lbuchman/m1-platform/documentation/Legacy Test Fixture Documentation/Project Notes/Trouble Shooting.docx

# Test Fixture Troubleshooting guide

This document provides information on how to trouble shoot the test fixture.

This document does not provide information on how to troubleshoot or repair M1-3200 boards. For M1-3200 help contact S2 hardware team.

Reference documents:

1. Test board Serial terminal.docx
2. Backend CLI.docx

# Testing the test fixture

The test fixture shall be tested with the know to work “Golden” M1-3200. Please have few Golden boards for the testing.

Run Commission Test from test fixture PC front end GUI application.

If error is reported follow the information below for the troubleshooting guide.

Error which will not produce printed Error labels

1. Hand help scanner issue - check USB cable, replace the scanner
2. Label printer – paper jam, USB cable, power supply, replace the label printer
3. Keyboard or mouse – check the battery, replace
4. Ethernet Error – check cables, check Sam-E, replace SAM-E
5. Test fixture power – check wiring, check power supply, replace power supply
6. USB Hub – verify the Hub is working, check wiring, replace the Hub
7. PC – contact LenelS2
8. PC has incorrect time, or Logs sync issues – check PC internet connection

Printed Error labels

Id | Error Code | Test | Remedy
ICT_EXCEPT | ICT-EXCEPTION | ICT | ICT test unexpected failure. Re-run the test. Contact S2
TP025 | 000000000TP25 | ICT | TP25 voltage is out of tolerance. TP25 voltage is out of tolerance Check wiring, troubleshoot or replace custom test board
TP33 | 000000000TP33 | ICT | TP33 voltage is out of tolerance Check wiring, troubleshoot or replace custom test board
TP35 | 000000000TP35 | ICT | TP35 voltage is out of tolerance Check wiring, troubleshoot or replace custom test board
TP34 | 000000000TP34 | ICT | TP34 voltage is out of tolerance Check wiring, troubleshoot or replace custom test board
TP36 | 000000000TP36 | ICT | TP36 voltage is out of tolerance Check wiring, troubleshoot or replace custom test board
TP31 | 000000000TP31 | ICT | TP31 voltage is out of tolerance Check wiring, troubleshoot or replace custom test board
J5.13 | 000000TPJ5.13 | ICT | Ribbon Cable J5.13 voltage is out of tolerance Check wiring, troubleshoot or replace custom test board
J5.8 | 0000000TPJ5.8 | ICT | Ribbon Cable J5.8 voltage is out of tolerance Check wiring, troubleshoot or replace custom test board
BatCellBat | 000000CoinBat | ICT | Coin Cell backup battery voltage is out of tolerance Check wiring, troubleshoot or replace custom test board
J5.18 | 000000TPJ5.18 | ICT | Ribbon Cable continuity failed Check wiring, troubleshoot or replace custom test board
J5.15 | 000000TPJ5.15 | ICT | Ribbon Cable continuity failed Check wiring, troubleshoot or replace custom test board
J5.17 | 000000TPJ5.17 | ICT | Ribbon Cable continuity failed Check wiring, troubleshoot or replace custom test board
J5.19 | 000000TPJ5.19 | ICT | Ribbon Cable continuity failed Check wiring, troubleshoot or replace custom test board
J5.16 | 000000TPJ5.16 | ICT | Ribbon Cable continuity failed Check wiring, troubleshoot or replace custom test board
J5.5 | 0000000TPJ5.5 | ICT | Ribbon Cable voltage is out of tolerance Check wiring, troubleshoot or replace custom test board
J5.6 | 0000000TPJ5.6 | ICT | Ribbon Cable voltage is out of tolerance Check wiring, troubleshoot or replace custom test board
J5.7 | 0000000TPJ5.7 | ICT | Ribbon Cable voltage is out of tolerance Check wiring, troubleshoot or replace custom test board
J5.14 | 000000TPJ5.14 | ICT | Ribbon Cable voltage is out of tolerance Check wiring, troubleshoot or replace custom test board
J5.23 | 000000TPJ5.23 | ICT | Ribbon Cable voltage is out of tolerance Check wiring, troubleshoot or replace custom test board
J5.25 | 000000TPJ5.25 | ICT | Ribbon Cable voltage is out of tolerance Check wiring, troubleshoot or replace custom test board
J5.20 | 000000TPJ5.20 | ICT | Ribbon Cable voltage is out of tolerance Check wiring, troubleshoot or replace custom test board
J5.22 | 000000TPJ5.22 | ICT | Ribbon Cable voltage is out of tolerance Check wiring, troubleshoot or replace custom test board
J5.24 | 000000TPJ5.24 | ICT | Ribbon Cable voltage is out of tolerance Check wiring, troubleshoot or replace custom test board
J5.26 | 000000TPJ5.26 | ICT | Ribbon Cable voltage is out of tolerance Check wiring, troubleshoot or replace custom test board
J8.2 | 0000000RedLed | ICT | J8.2 Red Led voltage drop is out of tolerance Check wiring, troubleshoot or replace custom test board
J8.1 | 0000000BlueLed | ICT | J8.1 Blue Led voltage drop is out of tolerance Check wiring, troubleshoot or replace custom test board
RS422 | 00000000RS422 | ICT | Ribbon Cable RS-422 echo test failed Check wiring, troubleshoot or replace custom test board
RS485 | 00000000RS485 | ICT | RS-485 echo test failed Check wiring, troubleshoot or replace custom test board
Tamper Pin | 0000000Tamper | ICT | Tamper pin test failed Check wiring, troubleshoot or replace custom test board
DDR3Bus | 0000DDR3-DBus | ICT | DDR3 data bus test failed Check wiring, troubleshoot or replace custom test board
DDR3ABus | 0000DDR3-ABus | ICT | DDR3 address bus test failed. This is not test fixture related error
DDR3 | 000000000DDR3 | ICT | DDR3 read/write verify test failed. This is not test fixture related error
EEPROM | 0000000EEPROM | ICT | EEPROM test failed
EEPROMUPDATE | 00UPD-0EEPROM | ICT | Update EEPROM with new data command failed. This is not test fixture related error
ATOP | 00BATT-SWITCH | ICT | Test Main power to battery power switching failed. Check wiring, troubleshoot or replace custom test board
BACH | 000BATT-CHARG | ICT | The Battery module charging voltage is out of tolerance. Check wiring, troubleshoot or replace custom test board
STM | 000000USB-DFU | ICT | Failed to program M1 bootstrap STM, RFU issue or BUT is down
APP80 | 00000APP-PING | APP | BUT Web server is down, possible APP is not running. This is not test fixture related error
FLASH | 0000000000FLASH | FLASH | Program FLASH failed. Check M1-3200 USB cable
MAC | 000000PROG-AMC | MAC | Program MAC failed. Check M1-3200 USB cable
MAC_CMP_ERR | 000MAC_CMP_ERR | FUN | If config reported MAC does not match OTP MAC This is not test fixture related error
PEN_DRIVE | 00000PEN_DRIVE | FUN | Pen drive failed. BUT USB Host port issue. Check USB cable. Replace Pen drive
RTC | 00000000000RTC | FUN | RTC test failed. This is not test fixture related error
SPI_RAM | 0000000SPI_RAM | FUN | SPI RAM test failed. This is not test fixture related error
FUN_EXCEPT | FUN-EXCEPTION | FUN | Functional test general failure. Contact LenelS2
WDT | 0000000000WDT | FUN | Watchdog test failed. This is not test fixture related error
BUT_ETHER | 0000UUT_ETHER | FUN | BUT not pingable, possibly Ethernet controller or cabling issue
BUT_TERM | 00000UUT_TERM | FUN | BUT terminal login error, check serial link, check FW/SW revisions. Replace USB cable, Replace RS232 to USB cable
SSH_BRECON | 0000SSH_BRECON | FUN | Ssh connection to BUT error, check wiring or cabling issue.
RFU_STM | 000000DFU_STM | FUN | Program bootstrap STM file to BUT over RFU error. Check wiring, replace M1-3200 USB cable
I2CBus1 | 00000I2C_BUS1 | FUN | I2C Bus 1 test failed. This is not test fixture related error
I2CBus02 | 0000I2C_BUS02 | FUN | I2C Bus 0,2 test failed. This is not test fixture related error
NO_OTP_MAC | 000NO_OTP_MAC | FUN | MAC Address is not programmed in OTP. This is not test fixture HW related error
SERIAL_MISMATCH | SER_MISS_MATCH | LABEL | Serial number provided does not match EEPROM value. Invalid serial number scanned in
FW_MISMATCH | FW_MISS_MATCH | LABEL | The BUT programmed FW Rev does not match FW File. Re-Commission the M1-3200
Lever Sensor | #NAME? | ICT | The Lock Lever is not locked
ERR_UNDER | 0000ERR_UNDER | Label | Undefined error, i.e. no error code available in the DB for this failure. Contact LenelS2
