lbuchman/m1-platform/documentation/Legacy Test Fixture Documentation/Project Notes/Testing Procedure.docx

Testing Procedure

1. Start the test fixture software

Double click M1-3200 launcher icon on the left side of the Desktop screen

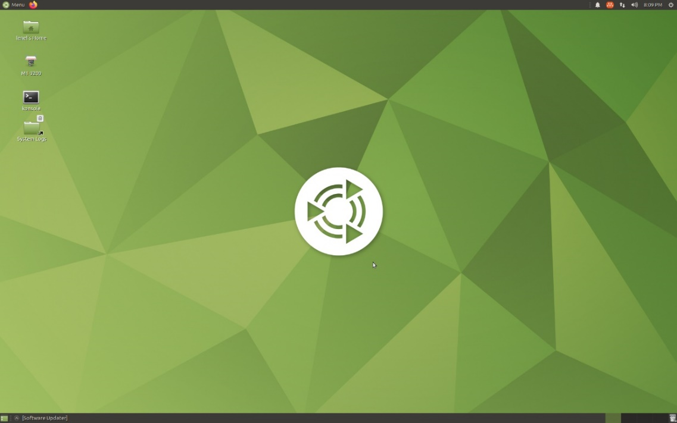
[picture p12: figure]
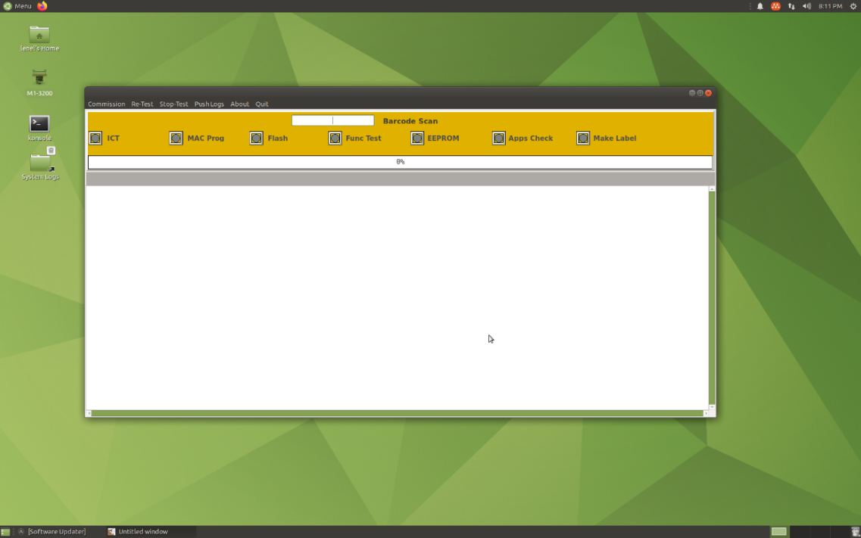
[picture p13: figure]

2. Open the test fixture cover.

Move the cover lever on the right site to the vertical position.

Using the cover handle on the front side of the fixture open the top cover

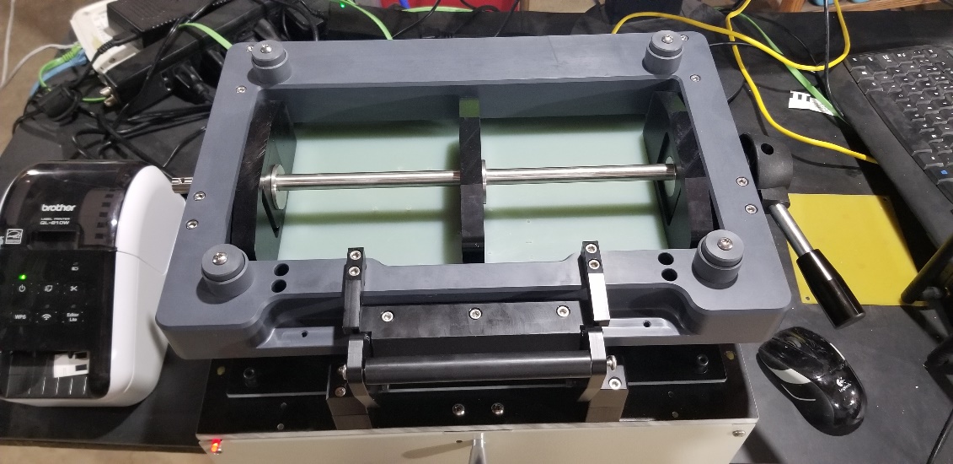
[picture p14: figure]
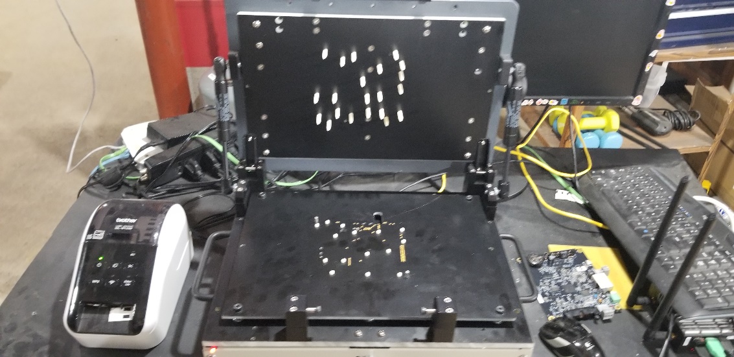
[picture p15: figure]

3. Place the M1-3200 board into the test fixture

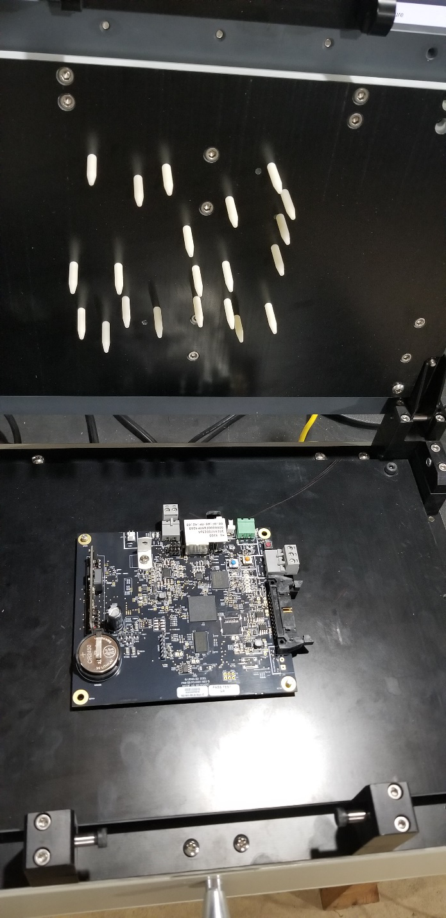
[picture p16: figure]

4. Scan the Serial Number barcode (the board front edge as shown above)

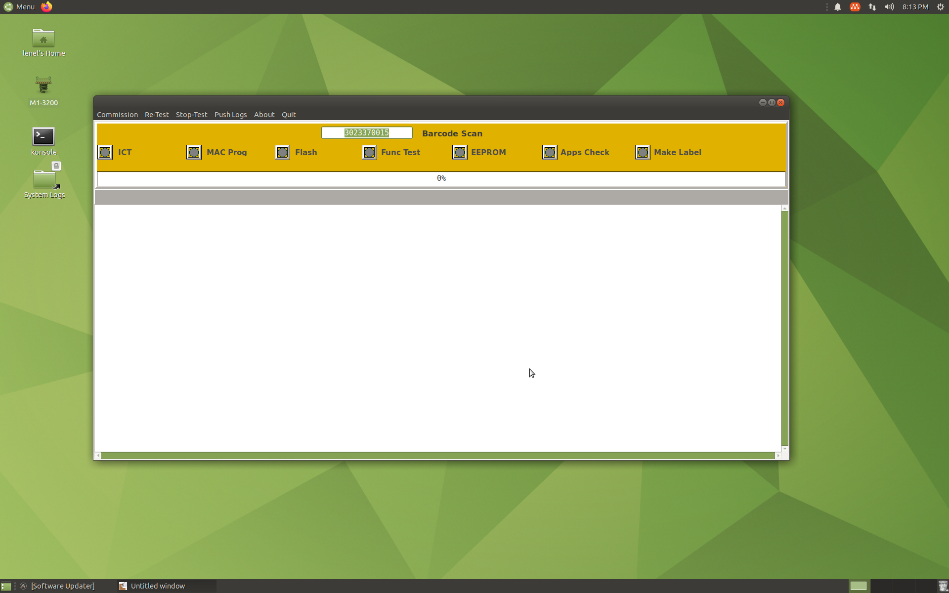
[picture p17: figure]

5. Close the test fixture cover.

Make sure to latch the lever handle on the side of the test fixture to the horizontal position.

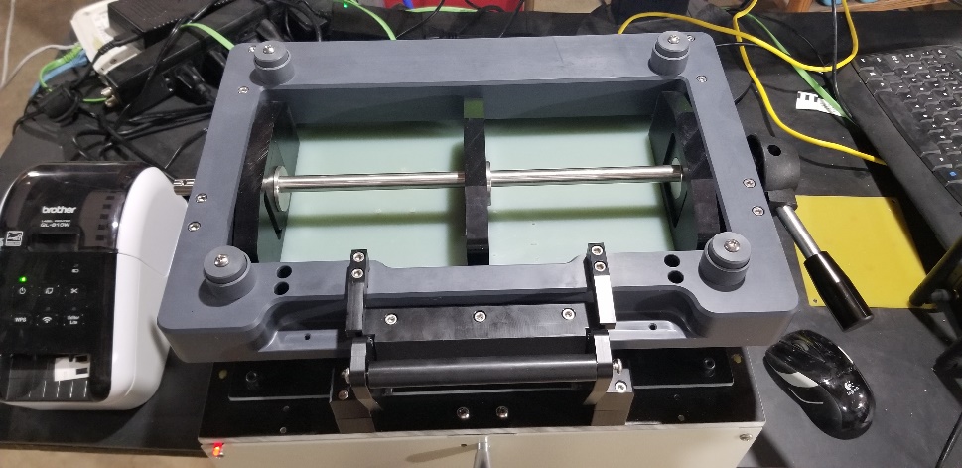
[picture p18: figure]

The Red LED shall be on when the latch lever is locked.

6. Press the desired action, Commission or Re-Test

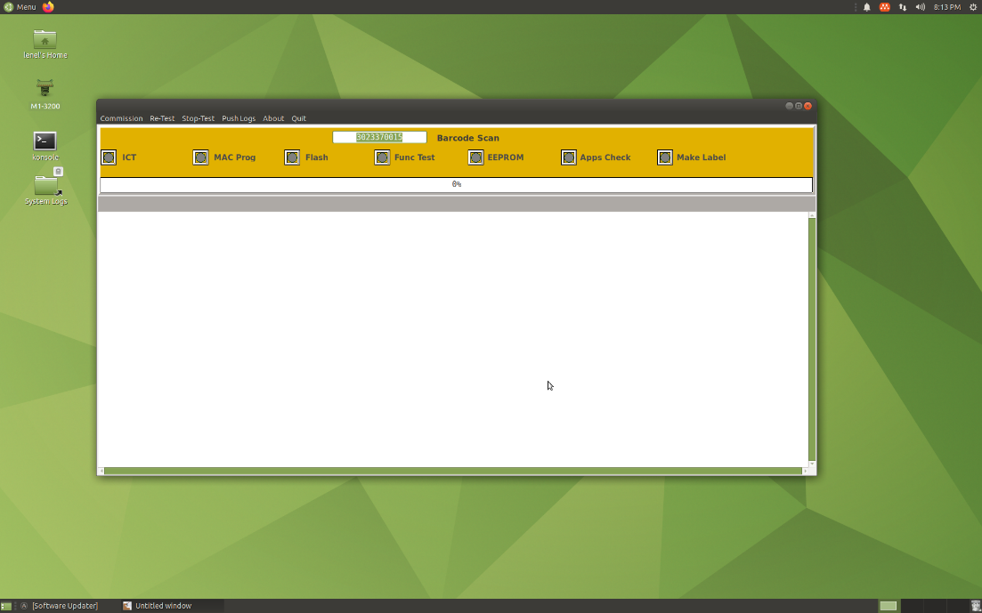
[picture p19: figure]

7. Wait until test is complete

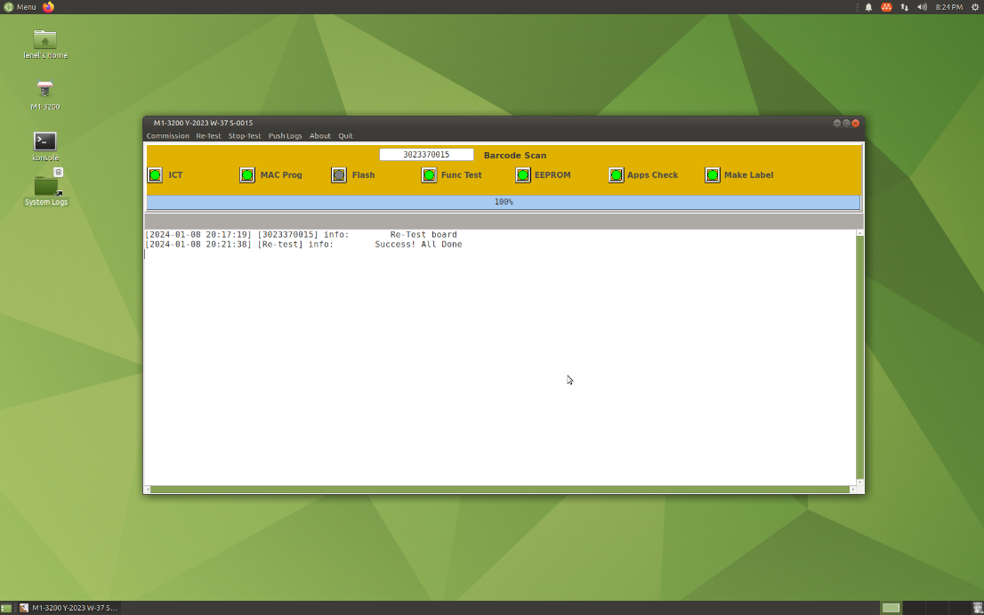
[picture p20: figure]

When complete the label is printed
