lbuchman/m1-platform/documentation/Legacy Test Fixture Documentation/Project Notes/TestPlan.xlsx

Sheet: Test Vectors
Notes | Test Vector # | Description | Purpose | UUT | Test Steps | Expected Result | Test Status
 | 1 | Pogo Pins Inspection | Visual Inspection |  | Open test fixture cover | There are no shorts between pogopins, wiring connections to pogo pins are secured. Wiring to test board terminals are robust. Wiring is well organized to harnesses. Use test fixture 1 pictures as a reference.
 | 2 | TF Wiring inspection | Visual Inspection |  | Open test fixture cover | The power supply wiring are secured and robust. No floating cables, ar connections are robust
Aggregated 42 test cases | 3 | Assembly integrity | Validate the pogo pins are connected to the proper I/O on the test board i.e. verifying the integrity of the electrical connections. There are 5 dozen of connections to check. This is time consuming operation. |  | Use multimeter and set it to the continuity function | Use Wiring map Tab and make sure all connection are correctly made.
 | 45 | Lever Switch test | Lever and Green Led test | Golden Board | 1. Lock the test fixture cover with the Lever handle 3. Execute Re-Test | The Green Led on the front panel of the test fixture shall be on. There shall be no error when test starts that Lever shall be locked before the test
 | 46 | Lever Switch test | Lever and Green Led test | Golden Board | 1. Do not Lock the test fixture cover with the Lever handle 3. Execute Re-Test | The error shall be reported that Lever is not locked
 | 47 | Power supply check | Correct power supply output |  | Use meter and measure power supply 12V and 5V output | The 12V output shall be at least 12.4V, 5V output shell be 5% accurate
 | 48 | Ethernet Internet Connection | Validate the cable is plugged from the PC to the TF | Golden Board | 1. Place the golden board into the fixture. 2. Disconnect ISP Ethernet cable from the PC 3. Execute Re-Test 4. When ICT Test Complete click Stop-Test | [2024-03-01 00:18:44] [3023200040, ict] error: Ethernet Internet jack is not plugged. Check connection and retry the test.
 | 49 | Ethernet Internet Connection | Validate the cable is plugged from the PC to the TF | Golden Board | 1. Place the golden board into the fixture. 2. Connect ISP Ethernet cable from the PC 3. Execute Re-Test 4. When ICT Test Complete click Stop-Test | No Error shall be reported
 | 50 | Ethernet PC/TF Connection | Validate the cable is plugged | Golden Board | 1. Place the golden board into the fixture. 2. Disconnect Ethernet cable from the TF 3. Execute Re-Test 4. When ICT Test Complete click Stop-Test | [2024-03-01 00:18:44] [3023200040, ict] error: M1-3200 Ethernet jack is not plugged. Check connection and retry the test.
 | 51 | Ethernet PC/TF Connection | Validate the cable is plugged | Golden Board | 1. Place the golden board into the fixture. 2. Connect Ethernet cable from the TF 3. Execute Re-Test 4. When ICT Test Complete click Stop-Test | No Error shall be reported
 | 52 | Label Printer Connection | Validate the cable is plugged | Golden Board | 1. Place the golden board into the fixture. 2. Disconnect label printer cable from the PC 3. Execute Re-Test 4. When ICT Test Complete click Stop-Test | [2024-03-01 01:07:24] [3023200040, ict] error: Label Printer is not detected. Check connections and power and retry the test.
 | 53 | Label Printer Connection | Validate the cable is plugged | Golden Board | 1. Place the golden board into the fixture. 2. Connect label printer cable from the 3. Execute Re-Test 4. When ICT Test Complete click Stop-Test | No Error shall be reported
 | 54 | Test Board Usb Link (Teensy connection) | Validate test board (Teensy board) is connected to the PC | Golden Board | 1. Place the golden board into the fixture. 2. Disconnect Teensy USB cable from the PC 3. Execute Re-Test 4. When ICT Test Complete click Stop-Test | [2024-03-01 23:24:06] [3023200040, ict] error: Test board Teensy is not found. Check connections and retry the test.
 | 55 | Test Board Usb Link (Teensy connection) | Validate test board (Teensy board) is connected to the PC | Golden Board | 1. Place the golden board into the fixture. 2. Connect Teensy USB cable to the PC 3. Execute Re-Test 4. When ICT Test Complete click Stop-Test | No Error shall be reported
Only USB to RS232 cable is tested by this test. | 56 | Test M1-3200 terminal serial link | Validate that USB to RS232 converter for M1-3200 terminal | Golden Board | 1. Place the golden board into the fixture. 2. Disconnect USB to RS232 cable from the PC 3. Execute Re-Test 4. When ICT Test Complete click Stop-Test | [2024-03-01 23:24:06] [3023200040, ict] error: M1-3200 Terminal Serial Converter is not found. Check connections and retry the test.
Only USB to RS232 cable is tested by this test. | 57 | Test M1-3200 terminal serial link | Validate that USB to RS232 converter for M1-3200 terminal | Golden Board | 1. Place the golden board into the fixture. 2. Connect USB to RS232 cable to the PC 3. Execute Re-Test 4. When ICT Test Complete click Stop-Test | No Error shall be reported
 | 58 | Cloud synch alert | Validate the GUI frontend displays alert is activated if logfiles are not synced to the Cloud | Golden Board | 1. Remote flagging file with the command: #sudo rm -f /home/lenel/m1mtf/*.txt. 2. Wait up to 1 min | The GUI shall display the blinking alert in Red in the upper left cornet. The warning shall read "Cloud Sync Failed for 7 days, contact LenelS2
 | 59 | Manual Cloud synch | Validate the GUI frontend displays alert is deactivated if logfiles are synced to the Cloud | Golden Board | 1. Execute test vector 11 2. Click main menu->Cloud->Push Logs 3. Click main menu->Cloud->Push Secrets | Wait up to 1 min, the blinking Red alert shall not be disabled
 | 60 | Automatic Cloud sync | Validate that logfiles and secrets are automatically updated qat night. | Golden Board | Execute test vector 11 | Wait overnight. Next day the blinking Red alert shall not be disabled
 | 61 | Serial Number validation | Validate the serial number entered is properly formatted | Golden Board | 1. Scan the serial number from M1-3200 2. Execute Re-Test | No Error shall be reported
 | 62 | Serial Number validation | Validate the serial number entered is properly formatted | Golden Board | 1. Enter 10 digits for the serial number, make sure the first two are not 30 2. Execute Re-Test | The Error pop-up with the message :Invalid Barcode" shall be displayed.
 | 63 | Duplicate serial number | Validate that serial number is unique | Golden Board | 1. Scan the serial number from M1-3200 2. Execute Re-Test 3. When ICT Test Complete click Stop-Test 4. Replace the Golden Board with another Golden board 5. Do not change the serial number 6. Execute Re-Test | The command shall failed with the message below. Executing program MAC command ... [2024-03-02 02:11:06] [3023200040, progmac] error: UNIQUE constraint failed: records.cpuSerial
 | 64 | PC SW update | Validate the PC can download updates from the Cloud | Golden Board | 1. execute cmd #rm -f /home/lenel/m1mtf/tmp/* 2. execute cmd #rm -f -f /home/lenel/m1mtf/fsb.l.stm32 3. execute cmd #rm -f -fr /home/lenel/m1mtf/stm32mp15-lenels2-m1 4. execute cmd #m1client update | 1 inspect directory /home/lenel/m1mtf, make sure fsb.l.stm32 and stm32mp15-lenels2-m1 are restored 2.inspect m1client std output. Make sure there is no any errors #m1client update [2024-03-02 01:55:32] [m1cli, update] info: Checking for SW & FW update ... [2024-03-02 01:55:32] [m1cli, update] info: Downloading manifestFile [2024-03-02 01:55:32] [m1cli, update] info: New FW is available [2024-03-02 01:55:32] [m1cli, update] info: sending kill to apps [2024-03-02 01:55:32] [m1cli, update] info: Downloading m1firmware.txz [2024-03-02 01:55:32] [m1cli, update] info: Downloading fsbl.stm32 [2024-03-02 01:55:32] [m1cli, update] info: Downloading m1tfd1_9caa16de_amd64.snap [2024-03-02 01:55:32] [m1cli, update] info: Downloading m1client_e8b7e7c2_amd64.snap [2024-03-02 01:55:37] [m1cli, update] info: Download complete, checking hashes [2024-03-02 01:55:38] [m1cli, update] info: Hashes are fine [2024-03-02 01:55:38] [m1cli, update] info: updating txz [2024-03-02 01:55:38] [m1cli, update] info: updating stm [2024-03-02 01:55:38] [m1cli, update] info: updating snap [2024-03-02 01:55:38] [m1cli, update] info: updating snapclient [2024-03-02 01:55:47] [m1cli, update] info: /home/lenel/m1mtf/UpdateFwTimeStamp.txt [2024-03-02 01:55:47] [m1cli, update] info: Done
 | 65 | MAC Programming | Validate that MAC is programmed | Golden Board | 1. You will need M1-3200 with no MAC programmed 2. In GUI press CNTR M to enable debug mode 2. Click "MAC Prog" LED | The shall be no error reported. If MAC was already programmed the MAC address will be reported
 | 66 | SSD programming | Validate that SSD is programmed | Golden Board | 1. You will need two different FW versions available for this test to validate that FW is programmed, or totally blank M1-3200. If FW was already programmed just use a different FW version 2. In GUI press CNTR M to enable debug mode 2. Click "Flash" LED | The shall be no error reported. When programming is done open the terminal and execute #picocom -b 115200 /dev/ttyUSB0. The login is root:only4u2c . Execute ifconfig and validate that MAC address is as expected.
 | 67 | Functional Test | This is automated SW based test. The test will use M1-3200 terminal and ssh session. This will test Ethernet, watchdog, RTC, I2C, EEPROM, USB Pen drive, and SPI RAM | Golden Board | 1. In GUI press CNTR M to enable debug mode 2. Click "Flash" LED | The shall be no error reported
 | 68 | EEPROM programming | Write EEPROM if EEPROM is blank or validate if not blank. | Golden Board | 1. In GUI press CNTR M to enable debug mode 2. Click "EEPROM" LED | The shall be no error reported
 | 69 | M1-3200 app status | Check M1-3200 FW app is running, i.e. the init status flag is set and app opens port 80 | Golden Board | 1. In GUI press CNTR M to enable debug mode 2. Click "Apps Check" LED | The shall be no error reported
 | 70 | Label print | Check if the label is printed | Golden Board | 1. In GUI press CNTR M to enable debug mode 2. Click "Make Lebel" LED | The shall be no error reported. Label shall be printed
 | 71 | Commision | Check the commission procedure works | Golden Board | 1. In GUI press CNTR SHIFT ALT 1 to enable info mode mode 2. Click "Commision" Menu" | No Error shall be reported. Label shall be printed
 | 72 | Re-Test | Check the re-test procedure works | Golden Board | 1. In GUI press CNTR SHIFT ALT 1 to enable info mode mode 2. Click "Re-Test" Menu" | No Error shall be reported. No Flash programming shall be done. Label shall be printed
 | 73 | Verify FW rev reporting | Verify that GUI reports proper FW rev |  | 1. Click menu "About" | M1 FW rev is reported. Snaps rev are reported. Validate that M1 FW Rev is correct. FW rev is in the FW directory home/lenel/m1mtf/stm32mp15-lenels2-m1/REVISION. Execute command in the terminal #snap lis. Validate Snaps rev.
 | 74 | Error label | Verify error label is printed |  | 1. Scan the serial number from M1-3200 2. Disconnetc Led connector, or Temper plugs from the testing board 2. Click Re-Test | The label with the error code is pronted. Verify that error displayed match the error.
 | 75 | TP25 | Verify that voltage level out of tolerance fails the test | Golden Board | Mask test point | Test fails, error label is printed
 | 76 | TP33 | Verify that voltage level out of tolerance fails the test | Golden Board | Mask test point | Test fails, error label is printed
 | 77 | TP35 | Verify that voltage level out of tolerance fails the test | Golden Board | Mask test point | Test fails, error label is printed
 | 78 | TP34 | Verify that voltage level out of tolerance fails the test | Golden Board | Mask test point | Test fails, error label is printed
 | 79 | TP36 | Verify that voltage level out of tolerance fails the test | Golden Board | Mask test point | Test fails, error label is printed
 | 80 | TP31 | Verify that voltage level out of tolerance fails the test | Golden Board | Mask test point | Test fails, error label is printed
 | 81 | TPJ5.13 | Verify that voltage level out of tolerance fails the test | Golden Board | Mask test point | Test fails, error label is printed
 | 82 | TPJ5.8 | Verify that voltage level out of tolerance fails the test | Golden Board | Mask test point | Test fails, error label is printed
 | 83 | CointBat PLUS mterminal | Verify that voltage level out of tolerance fails the test | Golden Board | Mask test point | Test fails, error label is printed
 | 84 | TPJ5.18 | Verify that voltage level out of tolerance fails the test | Golden Board | Mask test point | Test fails, error label is printed
 | 85 | TPJ5.15 | Verify that voltage level out of tolerance fails the test | Golden Board | Mask test point | Test fails, error label is printed
 | 86 | TPJ5.17 | Verify that voltage level out of tolerance fails the test | Golden Board | Mask test point | Test fails, error label is printed
 | 87 | TPJ5.19 | Verify that voltage level out of tolerance fails the test | Golden Board | Mask test point | Test fails, error label is printed
 | 88 | TPJ5.16 | Verify that voltage level out of tolerance fails the test | Golden Board | Mask test point | Test fails, error label is printed
 | 89 | TPJ5.5 | Verify that voltage level out of tolerance fails the test | Golden Board | Mask test point | Test fails, error label is printed
 | 90 | TPJ5.6 | Verify that voltage level out of tolerance fails the test | Golden Board | Mask test point | Test fails, error label is printed
 | 91 | TPJ5.7 | Verify that voltage level out of tolerance fails the test | Golden Board | Mask test point | Test fails, error label is printed
 | 92 | TPJ5.14 | Verify that voltage level out of tolerance fails the test | Golden Board | Mask test point | Test fails, error label is printed
 | 93 | TPJ5.23 | Verify that voltage level out of tolerance fails the test | Golden Board | Mask test point | Test fails, error label is printed
 | 94 | TPJ5.25 | Verify that voltage level out of tolerance fails the test | Golden Board | Mask test point | Test fails, error label is printed
 | 95 | TPJ5.20 | Verify that voltage level out of tolerance fails the test | Golden Board | Mask test point | Test fails, error label is printed
 | 96 | TPJ5.22 | Verify that voltage level out of tolerance fails the test | Golden Board | Mask test point | Test fails, error label is printed
 | 97 | TPJ5.24 | Verify that voltage level out of tolerance fails the test | Golden Board | Mask test point | Test fails, error label is printed
 | 98 | TPJ5.26 | Verify that voltage level out of tolerance fails the test | Golden Board | Mask test point | Test fails, error label is printed
 | 99 | RedLed Signal | Verify that voltage level out of tolerance fails the test | Golden Board | Mask test point | Test fails, error label is printed
 | 100 | BlueLed Signal | Verify that voltage level out of tolerance fails the test | Golden Board | Mask test point | Test fails, error label is printed
 | 101 | RS422, plus or minus | Verify that voltage level out of tolerance fails the test | Golden Board | Mask test point | Test fails, error label is printed
 | 102 | RS485, plus or minus | Verify that voltage level out of tolerance fails the test | Golden Board | Mask test point | Test fails, error label is printed
 | 103 | Temper, signal | Verify that voltage level out of tolerance fails the test | Golden Board | Mask test point | Test fails, error label is printed
 | 104 | LA Bat, Plus | Verify that voltage level out of tolerance fails the test | Golden Board | Mask test point | Test fails, error label is printed
 | 105 | Ethernet | Verify that voltage level out of tolerance fails the test | Golden Board | Mask test point | Test fails, error label is printed

Sheet: Wiring Map
M1-3200 | Wire, Gauge | Dest | Name | Voltage Level | Tolerance
PP TP025 | 24-26 | TB J6.2 | M1-3200 Internal VCC | 5V | 5%
PP TP33 | 24-26 | TB J6.7 | PMIC VCC_ANGL | 2.9V | 5%
PP TP35 | 24-26 | TB J6.6 | PMIC VCC_P3V3_AUX | 3.3V | 5%
PP TP34 | 24-26 | TB J J6.5 | PMIC VCC_P3V3 | 3.3V | 5%
PP TP31 | 24-26 | TB J J6.4 | PMIC VDD_DDR | 1.35V | 5%
PP TP36 | 24-26 | TB J J6.3 | PMIC VDD_CORE | 1.2V | 5%
PP J14.1 | 24-26 | TB J J6.1 | Coin Cell 3.0V backup battery | 3.3V | 15%
PP P3.2 | 24-26 | TB J J6.8 | Boot select, TB OD output | N/A | N/A
PP J5.9 | 24-26 | TB J J5.9 | Ribbon RS-422 | N/A | N/A
PP J5.10 | 24-26 | TB J J5.10 | Ribbon RS-422 | N/A | N/A
PP J5.11 | 24-26 | TB J J5.11 | Ribbon RS-422 | N/A | N/A
PP J5.12 | 24-26 | TB J J5.12 | Ribbon RS-422 | N/A | N/A
PP J5.18 | 24-26 | TB J J5.18 | Ribbon AIO_S0 | Log 0 or 1 | 0.8V/2.7V
PP J5.15 | 24-26 | TB J J5.15 | Ribbon AIO_S1 | Log 0 or 1 | 0.8V/2.7V
PP J5.16 | 24-26 | TB J J5.16 | Ribbon AIO_S2 | Log 0 or 1 | 0.8V/2.7V
PP J5.19 | 24-26 | TB J J5.19 | Ribbon AIO_S7 | Log 0 or 1 | 0.8V/2.7V
PP J5.17 | 24-26 | TB J J5.17 | Ribbon AIO_nRST | Log 0 or 1 | 0.8V/2.7V
PP J5.5 | 24-26 | TB J J5.5 | Ribbon VCC_P6V | 6V | 5%
PP J5.7 | 24-26 | TB J J5.7 | Ribbon VCC_P6V | 6V | 5%
PP J5.13 | 24-26 | TB J J5.13 | Ribbon VCC_P12V | 12V | 5%
PP J5.8 | 24-26 | TB J J5.8 | Ribbon VCC_P6V | 6V | 5%
PP J5.14 | 24-26 | TB J J5.14 | Ribbon VCC_P12V | 12V | 5%
PP J5.23 | 24-26 | TB J J5.23 | Ribbon Ground | 0V | 5%
PP J5.25 | 24-26 | TB J J5.25 | Ribbon Ground | 0V | 5%
PP J5.20 | 24-26 | TB J J5.20 | Ribbon Ground | 0V | 5%
PP J5.22 | 24-26 | TB J J5.22 | Ribbon Ground | 0V | 5%
PP J5.24 | 24-26 | TB J J5.24 | Ribbon Ground | 0V | 5%
PP J5.26 | 24-26 | TB J J5.26 | Ribbon Ground | 0V | 5%
PP J07.1 | 24 | TB J J10.1 | Incoming Power 12V | 12V | 5%
PP J07.2 | 24 | TB J J10.2 | Incoming Power Ground | N/A | N/A
PP J08.1 | 24-26 | TB J J9.1 | Tamper Ground | N/A | N/A
PP J08.2 | 24-26 | TB J J9.2 | Tamper Signal | Log 0 or 1 | 0.8V/2.7V
PP J02.1 | 24-26 | TB J J8.1 | Led Blue | -2.6V:-3.3V | 5%
PP J02.1 | 24-26 | TB J J7.1 | Led Red | 1.6V:2.2V | 5%
PP J27.1 | 24-26 | TB J J1.8 | RS-485 DP | N/A | N/A
PP J27.2 | 24-26 | TB J J1.7 | RS-485 DN | N/A | N/A
PP J06.1 | 24 | TB J11.1 | Incoming Battery +12V | >11V | N/A
PP J06.2 | 24 | TB J11.2 | Incoming Battery Ground | N/A | N/A
J13 |  |  | M1-3200 USB Mini DFU port | N/A | N/A
 |  |  | Connected to PC USB port
J11 |  |  | M1-3200 Ethernet port
 |  |  | Connected to PC Ethernet port 1
PP J25.4 | 24 | DT-6554 Pin 4 | Debug Port Rx, DT-6554 is Connected to PC USB port | N/A | N/A
PP J25.5 | 24 | DT-6554 Pin 5 | Debug Port Tx, DT-6554 is Connected to PC USB port | N/A | N/A
Teensy 4.1 USB Port |  |  | Connected to PC USB port | N/A | N/A
3-D Scanner |  |  | Connected to PC USB port | N/A | N/A
Label Printer |  |  | Connected to PC USB port | N/A | N/A
PC Ethernet port 2 |  |  | Connected to Internet | N/A | N/A
