lbuchman/m1-platform/documentation/Legacy Test Fixture Documentation/Saline-Provided-M1-3200-TestFixtureDoc/Drill-M1-3200-1, M1 Test Fixture Drill Chart - Push Plate.xlsx

M1 Test Fixture Drill Chart, Push Plate
Drawing No. Drill-M1-3200-1
2024-04-30
zero x zero: X = 4.00" from left alignment hole, Y = -2.25" from left alignment hole
Push Plate, Pressure Fingers | Location |  | Hole size
 | X | Y | Dia 1/8"
 | 0.05 | 4.00
 | 0.65 | 4.40
 | 1.95 | 3.90
 | 2.95 | 3.55
 | 1.65 | 4.32
 | 1.15 | 3.61
 | 3.75 | 3.60
 | 4.05 | 4.10
 | 4.85 | 3.70
 | 4.75 | 2.00
 | 4.75 | 1.20
 | 4.75 | 0.60
 | 4.35 | 0.00
 | 4.07 | 0.12
 | 3.5 | 0.83
 | 2.57 | 1.60
 | 2.03 | 0.15
 | 3.59 | 2.50
 | 2.86 | 2.65
 | 0.98 | 2.66
 | -0.07 | 2.67
 | 1.42 | 0.44
 | 0.44 | 0.03
