lbuchman/m1-platform/documentation/Legacy Test Fixture Documentation/Saline-Provided-M1-3200-TestFixtureDoc/Drill-M1-3200-2, M1 Test Fixture Drill Chart - Stripper Plate.xlsx

M1 Test Fixture Drill Chart, Stripper Plate
Drawing No. Drill-M1-3200-2
2023-04-30
zero x zero: X = 4.00" from left alignment hole, Y = -2.25" from left alignment hole |  |  |  | Alignment holes | Location
 |  |  |  | Hole size, diam=0.171" | X | Y
 |  |  |  | MTG1 | 5.05 | 0
Stripper Plate clearance holes | Hole size | Location |  | MTG2 | 0 | 0
 | diameter=0.10" |  |  | MTG3 | 0 | 4.35
 |  |  |  | MTG4 | 5.05 | 4.35
Signal | TP | X | Y
PNL LED | J02.1 | 1.2100 | 4.3700
PNL LED | J02.2 | 1.3100 | 4.3700 | Cut outs | Cutout corners
VCC_P12V_BATT | J06.1 | 2.4500 | 4.2717 |  | X | Y
BATT_GND | J06.2 | 2.2500 | 4.2717 | nut | 1.45 | 3.75
TXP | J11.1 | 3.1950 | 3.8750 |  | 1.45 | 3.45
TXN | J11.2 | 3.1450 | 3.7750 |  | 1.75 | 3.45
RXP | J11.3 | 3.0950 | 3.8750 |  | 1.75 | 3.75
TD- | J11.4 | 3.0450 | 3.7750
RXCT | J11.5 | 2.9950 | 3.8750 | J13 | 3.45 | 4.64
RXN | J11.6 | 2.9450 | 3.7750 |  | 3.45 | 4.25
N/C | J11.7 | 2.8950 | 3.8750 |  | 3.94 | 4.25
ETH_GND | J11.8 | 2.8450 | 3.7750 |  | 3.94 | 4.64
VBUS | J12.1 | 3.7001 | 4.0909
DN | J12.2 | 3.7001 | 4.0121
DP | J12.3 | 3.7001 | 3.9334 | PCB stops | Location
GND | J12.4 | 3.7001 | 3.8546 | Hole size, diam=1/8" | X | Y
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
