lbuchman/m1-platform/documentation/Legacy Test Fixture Documentation/Saline-Provided-M1-3200-TestFixtureDoc/Drill-M1-3200-3, M1 Test Fixture Drill Chart - Probe Plate.xlsx

M1 Test Fixture Drill Chart, Probe Plate
Drawing No. Drill-M1-3200-3
2023-04-30
zero x zero: X = 4.00" from left alignment hole, Y = -2.25" from left alignment hole |  |  |  | Alignment holes | Location
 |  |  |  | Hole size, diam=0.171" | X | Y
 |  |  |  | MTG1 | 5.05 | 0
Probe Plate socket holes | Hole size |  |  | MTG2 | 0 | 0
 | diam=0.068" |  |  | MTG3 | 0 | 4.35
 |  |  |  | MTG4 | 5.05 | 4.35
Signal | TP | X | Y
PNL LED | J02.1 | 1.2100 | 4.3700
PNL LED | J02.2 | 1.3100 | 4.3700
VCC_P12V_BATT | J06.1 | 2.4500 | 4.2717
BATT_GND | J06.2 | 2.2500 | 4.2717
TXP | J11.1 | 3.1950 | 3.8750
TXN | J11.2 | 3.1450 | 3.7750
RXP | J11.3 | 3.0950 | 3.8750
TD- | J11.4 | 3.0450 | 3.7750
RXCT | J11.5 | 2.9950 | 3.8750
RXN | J11.6 | 2.9450 | 3.7750
N/C | J11.7 | 2.8950 | 3.8750
ETH_GND | J11.8 | 2.8450 | 3.7750
VBUS | J12.1 | 3.7001 | 4.0909
DN | J12.2 | 3.7001 | 4.0121
DP | J12.3 | 3.7001 | 3.9334
GND | J12.4 | 3.7001 | 3.8546
GND | J08.1 | 4.0201 | 4.3750
NTAMPER | J08.2 | 4.1201 | 4.3750
P12V_RAW | J07.1 | 4.5860 | 4.2717
GND | J07.2 | 4.3860 | 4.2717
RS485_DP | J27.1 | 4.9800 | 3.0900
RS485_DN | J27.2 | 4.9800 | 3.2900
GND | J05.1 | 4.9000 | 2.4000
GND | J05.2 | 5.0000 | 2.4000
I2C1_SCL_DRV | J05.3 | 4.9000 | 2.3000
GND | J05.4 | 5.0000 | 2.3000
VCC_P6V | J05.5 | 4.9000 | 2.2000
I2C1_SDA_DRV | J05.6 | 5.0000 | 2.2000
VCC_P6V | J05.7 | 4.9000 | 2.1000
VCC_P6V | J05.8 | 5.0000 | 2.1000
RS485_RN | J05.9 | 4.9000 | 2.0000
RS485_RP | J05.10 | 5.0000 | 2.0000
RS485_XN | J05.11 | 4.9000 | 1.9000
RS485_XP | J05.12 | 5.0000 | 1.9000
VCC_P12V_MAIN | J05.13 | 4.9000 | 1.8000
VCC_P12V_MAIN | J05.14 | 5.0000 | 1.8000
AIO_S1 | J05.15 | 4.9000 | 1.7000
AIO_S2 | J05.16 | 5.0000 | 1.7000
AIO_nRST | J05.17 | 4.9000 | 1.6000
AIO_S0 | J05.18 | 5.0000 | 1.6000
AIO_SEL7 | J05.19 | 4.9000 | 1.5000
GND | J05.20 | 5.0000 | 1.5000
GND | J05.21 | 4.9000 | 1.4000
GND | J05.22 | 5.0000 | 1.4000
GND | J05.23 | 4.9000 | 1.3000
GND | J05.24 | 5.0000 | 1.3000
GND | J05.25 | 4.9000 | 1.2000
GND | J05.26 | 5.0000 | 1.2000
VCC_P3V_COIN | J14.1 | 0.4214 | 1.4505
VCC_P5V_PS | TP025 | 1.8336 | 2.1628
VCC_ANLG | TP33 | 2.6232 | 3.6544
VCC_P3V3A | TP34 | 3.9551 | 2.8150
VCC_P3V3_AUX | TP35 | 2.2301 | 2.7950
VDD_DDR | TP31 | 2.5992 | 1.1624
VDD_CORE | TP36 | 2.4850 | 2.9150
GND, Serial Terminal | J25.1 | 1.9800 | 1.3400
N/C | J25.2 | 1.9800 | 1.2400
N/C | J25.3 | 1.9800 | 1.1400
CN_UART0_RXD, Serial Terminal | J25.4 | 1.9800 | 1.0400
CN_UART0_TXD, Serial Terminal | J25.5 | 1.9800 | 0.9400
N/C | J25.6 | 1.9800 | 0.8400
MP1_BOOT1 | P3.2 | 2.4356 | 3.8450
USB0_DC | TP113 | 3.3250 | 3.4950
CPU_USB0_ID | TP114 | 3.3816 | 3.5488
 | Hole size
 | diam=0.054"
CPU_USB0_DP J13.3 | TP119 | 3.7120 | 4.2210
CPU_USB0_DM J13.2 | TP111 | 3.6500 | 4.2450
